QDaniel/ESPuino/src/Bluetooth.cpp

#include <Arduino.h>
#include "settings.h"

#include "Bluetooth.h"

#include "Common.h"
#include "Log.h"
#include "RotaryEncoder.h"
#include "System.h"

#include <AudioPlayer.h>

#ifdef BLUETOOTH_ENABLE
	#include "esp_bt.h"
	#include "BluetoothA2DPCommon.h"
	#include "BluetoothA2DPSink.h"
	#include "BluetoothA2DPSource.h"
	#if (defined(ESP_ARDUINO_VERSION_MAJOR) && (ESP_ARDUINO_VERSION_MAJOR >= 3))
		#include "ESP_I2S.h"
I2SClass i2s;
	#endif
#endif

#ifdef BLUETOOTH_ENABLE
	#define BLUETOOTHPLAYER_VOLUME_MAX 21u
	#define BLUETOOTHPLAYER_VOLUME_MIN 0u

BluetoothA2DPSink *a2dp_sink;
BluetoothA2DPSource *a2dp_source;
RingbufHandle_t audioSourceRingBuffer;
String btDeviceName;
#endif

#ifdef BLUETOOTH_ENABLE
const char *getType() {
	if (System_GetOperationMode() == OPMODE_BLUETOOTH_SINK) {
		return "sink";
	} else {
		return "source";
	}
}
#endif

#ifdef BLUETOOTH_ENABLE
// for esp_a2d_connection_state_t see https://docs.espressif.com/projects/esp-idf/en/latest/esp32/api-reference/bluetooth/esp_a2dp.html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
void connection_state_changed(esp_a2d_connection_state_t state, void *ptr) {
	Log_Printf(LOGLEVEL_INFO, "Bluetooth %s => connection state: %s (Free heap: %u Bytes)", getType(), ((BluetoothA2DPCommon *) ptr)->to_str(state), ESP.getFreeHeap());
	if (System_GetOperationMode() == OPMODE_BLUETOOTH_SINK) {
		// for Neopixel (indicator LEDs) use the webstream mode
		gPlayProperties.isWebstream = false;
		gPlayProperties.pausePlay = false;
		gPlayProperties.playlistFinished = true;
	}
}
#endif

#ifdef BLUETOOTH_ENABLE
// for esp_a2d_audio_state_t see https://docs.espressif.com/projects/esp-idf/en/latest/esp32/api-reference/bluetooth/esp_a2dp.html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
void audio_state_changed(esp_a2d_audio_state_t state, void *ptr) {
	Log_Printf(LOGLEVEL_INFO, "Bluetooth %s => audio state: %s (Free heap: %u Bytes)", getType(), ((BluetoothA2DPCommon *) ptr)->to_str(state), ESP.getFreeHeap());
	if (System_GetOperationMode() == OPMODE_BLUETOOTH_SINK) {
		// set play/pause status
		gPlayProperties.pausePlay = (state != ESP_A2D_AUDIO_STATE_STARTED);
		// for Neopixel (indicator LEDs) use the webstream mode
		gPlayProperties.playlistFinished = false;
		gPlayProperties.isWebstream = true;
	}
}
#endif

#ifdef BLUETOOTH_ENABLE
// handle Bluetooth AVRC metadata
// https://docs.espressif.com/projects/esp-idf/en/release-v3.2/api-reference/bluetooth/esp_avrc.html
void avrc_metadata_callback(uint8_t id, const uint8_t *text) {
	if (strlen((char *) text) == 0) {
		return;
	}
	switch (id) {
		case ESP_AVRC_MD_ATTR_TITLE:
			// title
			Log_Printf(LOGLEVEL_DEBUG, "Bluetooth => AVRC Title: %s", text);
			break;
		case ESP_AVRC_MD_ATTR_ARTIST:
			// artists
			Log_Printf(LOGLEVEL_DEBUG, "Bluetooth => AVRC Artist: %s", text);
			break;
		case ESP_AVRC_MD_ATTR_ALBUM:
			// album
			Log_Printf(LOGLEVEL_DEBUG, "Bluetooth => AVRC Album: %s", text);
			break;
		case ESP_AVRC_MD_ATTR_TRACK_NUM:
			// current track number
			Log_Printf(LOGLEVEL_DEBUG, "Bluetooth => AVRC Track-No: %s", text);
			break;
		case ESP_AVRC_MD_ATTR_NUM_TRACKS:
			// number of tracks in playlist
			Log_Printf(LOGLEVEL_DEBUG, "Bluetooth => AVRC Number of tracks: %s", text);
			break;
		case ESP_AVRC_MD_ATTR_GENRE:
			// genre
			Log_Printf(LOGLEVEL_DEBUG, "Bluetooth => AVRC Genre: %s", text);
			break;
		default:
			// unknown/unsupported metadata
			Log_Printf(LOGLEVEL_DEBUG, "Bluetooth => AVRC metadata rsp: attribute id 0x%x, %s", id, text);
			break;
	}
}
#endif

#ifdef BLUETOOTH_ENABLE
// feed the A2DP source with audio data
int32_t get_data_channels(Frame *frame, int32_t channel_len) {
	if (channel_len < 0 || frame == NULL) {
		return 0;
	}
	// Receive data from ring buffer
	size_t len {};
	vRingbufferGetInfo(audioSourceRingBuffer, nullptr, nullptr, nullptr, nullptr, &len);
	if (len < (channel_len * 4)) {
		// Serial.println("Bluetooth source => not enough data");
		return 0;
	};
	size_t sampleSize = 0;
	uint8_t *sampleBuff;
	sampleBuff = (uint8_t *) xRingbufferReceiveUpTo(audioSourceRingBuffer, &sampleSize, (TickType_t) portMAX_DELAY, channel_len * 4);
	if (sampleBuff != NULL) {
		// fill the channel data
		for (int sample = 0; sample < (channel_len); ++sample) {
			frame[sample].channel1 = (sampleBuff[sample * 4 + 3] << 8) | sampleBuff[sample * 4 + 2];
			frame[sample].channel2 = (sampleBuff[sample * 4 + 1] << 8) | sampleBuff[sample * 4];
		};
		vRingbufferReturnItem(audioSourceRingBuffer, (void *) sampleBuff);
	};
	// avoid WDT reset & give audio/other tasks some CPU time
	vTaskDelay(portTICK_PERIOD_MS * 1);
	return channel_len;
};
#endif

#ifdef BLUETOOTH_ENABLE
// callback which is notified on update Receiver RSSI
void rssi(esp_bt_gap_cb_param_t::read_rssi_delta_param &rssiParam) {
	Log_Printf(LOGLEVEL_DEBUG, "Bluetooth => RSSI value: %d", rssiParam.rssi_delta);
}
#endif

#ifdef BLUETOOTH_ENABLE
// Callback notifying BT-source devices available.
// Return true to connect, false will continue scanning
bool scan_bluetooth_device_callback(const char *ssid, esp_bd_addr_t address, int rssi) {
	Log_Printf(LOGLEVEL_INFO, "Bluetooth source => Device found: %s", ssid);

	if (btDeviceName == "") {
		// no device name given, connect to first device found
		return true;
	} else {
		// connect if device name (partially) matching, todo: compare case insensitive here?
		return startsWith(ssid, btDeviceName.c_str());
	}
}
#endif

void Bluetooth_VolumeChanged(int _newVolume) {
#ifdef BLUETOOTH_ENABLE
	if ((_newVolume < 0) || (_newVolume > 0x7F)) {
		return;
	}
	// map bluetooth volume (0..127) to ESPuino volume (0..21) to
	uint8_t _volume;
	_volume = map(_newVolume, 0, 0x7F, BLUETOOTHPLAYER_VOLUME_MIN, BLUETOOTHPLAYER_VOLUME_MAX);
	if (AudioPlayer_GetCurrentVolume() != _volume) {
		Log_Printf(LOGLEVEL_INFO, "Bluetooth => volume changed:  %d !", _volume);
		AudioPlayer_VolumeToQueueSender(_volume, true);
	}
#endif
}

void Bluetooth_Init(void) {
#ifdef BLUETOOTH_ENABLE
	if (System_GetOperationMode() == OPMODE_BLUETOOTH_SINK) {
		// bluetooth in sink mode (player acts as a BT-Speaker)
		a2dp_sink = new BluetoothA2DPSink();
	#if (defined(ESP_ARDUINO_VERSION_MAJOR) && (ESP_ARDUINO_VERSION_MAJOR >= 3))
		i2s.setPins(I2S_BCLK, I2S_LRC, I2S_DOUT);
		if (!i2s.begin(I2S_MODE_STD, 44100, I2S_DATA_BIT_WIDTH_16BIT, I2S_SLOT_MODE_STEREO, I2S_STD_SLOT_BOTH)) {
			Log_Println("Failed to initialize I2S!", LOGLEVEL_ERROR);
			while (1)
				; // do nothing
		}
		a2dp_sink->set_output(i2s);
	#else
		i2s_pin_config_t pin_config = {
		#if ESP_IDF_VERSION >= ESP_IDF_VERSION_VAL(4, 0, 0)
			.mck_io_num = 0,
		#endif
			.bck_io_num = I2S_BCLK,
			.ws_io_num = I2S_LRC,
			.data_out_num = I2S_DOUT,
			.data_in_num = I2S_PIN_NO_CHANGE
		};
		a2dp_sink->set_pin_config(pin_config);
	#endif
		a2dp_sink->set_rssi_callback(rssi);
		a2dp_sink->activate_pin_code(false);
		if (gPrefsSettings.getBool("playMono", false)) {
			a2dp_sink->set_mono_downmix(true);
		}
		a2dp_sink->set_auto_reconnect(true);
		a2dp_sink->set_rssi_active(true);
		// start bluetooth sink
		a2dp_sink->start(nameBluetoothSinkDevice);
		Log_Printf(LOGLEVEL_INFO, "Bluetooth sink started, Device: %s", nameBluetoothSinkDevice);
		// connect events after startup
		a2dp_sink->set_on_connection_state_changed(connection_state_changed, a2dp_sink);
		a2dp_sink->set_on_audio_state_changed(audio_state_changed, a2dp_sink);
		a2dp_sink->set_avrc_metadata_callback(avrc_metadata_callback);
		a2dp_sink->set_on_volumechange(Bluetooth_VolumeChanged);
	} else if (System_GetOperationMode() == OPMODE_BLUETOOTH_SOURCE) {
		// create audio source ringbuffer on demand
		audioSourceRingBuffer = xRingbufferCreate(8192, RINGBUF_TYPE_BYTEBUF);
		if (audioSourceRingBuffer == NULL) {
			Log_Println("cannot create audioSourceRingBuffer!", LOGLEVEL_ERROR);
		}
		//  setup BT source
		a2dp_source = new BluetoothA2DPSource();

		// a2dp_source->set_auto_reconnect(false);   // auto reconnect
		// a2dp_source->set_task_core(1);            // task core
		// a2dp_source->set_nvs_init(true);          // erase/initialize NVS
		// a2dp_source->set_ssp_enabled(true);       // enable secure simple pairing

		// pairing pin-code, see https://forum.espuino.de/t/neues-feature-bluetooth-kopfhoerer/1293/30
		String btPinCode = gPrefsSettings.getString("btPinCode", "");
		if (btPinCode != "") {
			a2dp_source->set_ssp_enabled(true);
			a2dp_source->set_pin_code(btPinCode.c_str());
		}
		// start bluetooth source
		a2dp_source->set_ssid_callback(scan_bluetooth_device_callback);
		a2dp_source->start(get_data_channels);
		// get device name
		btDeviceName = "";
		if (gPrefsSettings.isKey("btDeviceName")) {
			btDeviceName = gPrefsSettings.getString("btDeviceName", "");
		}
		Log_Printf(LOGLEVEL_INFO, "Bluetooth source started, connect to device: '%s'", (btDeviceName == "") ? "connect to first device found" : btDeviceName.c_str());
		// connect events after startup
		a2dp_source->set_on_connection_state_changed(connection_state_changed, a2dp_source);
		a2dp_source->set_on_audio_state_changed(audio_state_changed, a2dp_source);
		// max headphone volume (0..255): volume is controlled by audio class
		a2dp_source->set_volume(127);
	} else {
		esp_bt_mem_release(ESP_BT_MODE_BTDM);
	}
#endif
}

void Bluetooth_Cyclic(void) {
#ifdef BLUETOOTH_ENABLE
	if ((System_GetOperationMode() == OPMODE_BLUETOOTH_SINK) && (a2dp_sink)) {
		esp_a2d_audio_state_t state = a2dp_sink->get_audio_state();
		// Reset Sleep Timer when audio is playing
		if (state == ESP_A2D_AUDIO_STATE_STARTED) {
			System_UpdateActivityTimer();
		}
	}
	if ((System_GetOperationMode() == OPMODE_BLUETOOTH_SOURCE) && (a2dp_source)) {
		esp_a2d_audio_state_t state = a2dp_source->get_audio_state();
		// Reset Sleep Timer when audio is playing
		if (state == ESP_A2D_AUDIO_STATE_STARTED) {
			System_UpdateActivityTimer();
		}
	}
#endif
}

void Bluetooth_PlayPauseTrack(void) {
#ifdef BLUETOOTH_ENABLE
	if ((System_GetOperationMode() == OPMODE_BLUETOOTH_SINK) && (a2dp_sink)) {
		esp_a2d_audio_state_t state = a2dp_sink->get_audio_state();
		if (state == ESP_A2D_AUDIO_STATE_STARTED) {
			a2dp_sink->play();
		} else {
			a2dp_sink->pause();
		}
	}
#endif
}

void Bluetooth_NextTrack(void) {
#ifdef BLUETOOTH_ENABLE
	if ((System_GetOperationMode() == OPMODE_BLUETOOTH_SINK) && (a2dp_sink)) {
		a2dp_sink->next();
	}
#endif
}

void Bluetooth_PreviousTrack(void) {
#ifdef BLUETOOTH_ENABLE
	if ((System_GetOperationMode() == OPMODE_BLUETOOTH_SINK) && (a2dp_sink)) {
		a2dp_sink->previous();
	}
#endif
}

// set volume from ESPuino to phone needs at least Arduino ESP version 2.0.0
void Bluetooth_SetVolume(const int32_t _newVolume, bool reAdjustRotary) {
#ifdef BLUETOOTH_ENABLE
	if (!a2dp_sink) {
		return;
	}
	uint8_t _volume;
	if (_newVolume < int32_t(BLUETOOTHPLAYER_VOLUME_MIN)) {
		return;
	} else if (_newVolume > BLUETOOTHPLAYER_VOLUME_MAX) {
		return;
	} else {
		// map ESPuino min/max volume (0..21) to bluetooth volume (0..127)
		_volume = map(_newVolume, BLUETOOTHPLAYER_VOLUME_MIN, BLUETOOTHPLAYER_VOLUME_MAX, 0, 0x7F);
		a2dp_sink->set_volume(_volume);
		if (reAdjustRotary) {
			RotaryEncoder_Readjust();
		}
	}
#endif
}

bool Bluetooth_Source_SendAudioData(int16_t *outBuff, uint16_t validSamples) {
#ifdef BLUETOOTH_ENABLE
	// send audio data to ringbuffer
	if ((System_GetOperationMode() == OPMODE_BLUETOOTH_SOURCE) && (a2dp_source) && (validSamples > 0) && a2dp_source->is_connected()) {
		return (pdTRUE == xRingbufferSend(audioSourceRingBuffer, outBuff, sizeof(uint32_t) * validSamples, (TickType_t) portMAX_DELAY));
	} else {
		return false;
	}
#else
	return false;
#endif
}

bool Bluetooth_Device_Connected() {
#ifdef BLUETOOTH_ENABLE
	// send audio data to ringbuffer
	return (((System_GetOperationMode() == OPMODE_BLUETOOTH_SINK) && (a2dp_sink) && a2dp_sink->is_connected()) || ((System_GetOperationMode() == OPMODE_BLUETOOTH_SOURCE) && (a2dp_source) && a2dp_source->is_connected()));
#else
	return false;
#endif
}
