QDaniel/ESPuino/src/System.cpp

#include <Arduino.h>
#include "settings.h"

#include "System.h"

#include "Audio.h"
#include "AudioPlayer.h"
#include "Led.h"
#include "Log.h"
#include "Mqtt.h"
#include "Port.h"
#include "Power.h"
#include "Rfid.h"
#include "SdCard.h"
#include "esp_system.h"
#include "freertos/FreeRTOS.h"
#include "freertos/task.h"

#include <esp_random.h>

constexpr const char prefsRfidNamespace[] = "rfidTags"; // Namespace used to save IDs of rfid-tags
constexpr const char prefsSettingsNamespace[] = "settings"; // Namespace used for generic settings

Preferences gPrefsRfid;
Preferences gPrefsSettings;

unsigned long System_LastTimeActiveTimestamp = 0u; // Timestamp of last user-interaction
unsigned long System_SleepTimerStartTimestamp = 0u; // Flag if sleep-timer is active
bool System_GoToSleep = false; // Flag for turning uC immediately into deepsleep
bool System_Sleeping = false; // Flag for turning into deepsleep is in progress
bool System_LockControls = false; // Flag if buttons and rotary encoder is locked
uint8_t System_MaxInactivityTime = 10u; // Time in minutes, after uC is put to deep sleep because of inactivity (and modified later via GUI)
uint8_t System_SleepTimer = 30u; // Sleep timer in minutes that can be optionally used (and modified later via MQTT or RFID)

// Operation Mode
volatile uint8_t System_OperationMode;

void System_SleepHandler(void);
void System_DeepSleepManager(void);

// Init only NVS required for LPCD
void System_Init_LPCD(void) {
#ifdef PN5180_ENABLE_LPCD
	gPrefsRfid.begin(prefsRfidNamespace);
#endif
}

void System_Init(void) {
	srand(esp_random());

#ifndef PN5180_ENABLE_LPCD
	gPrefsRfid.begin(prefsRfidNamespace);
#endif
	gPrefsSettings.begin(prefsSettingsNamespace);

	// Get maximum inactivity-time from NVS
	uint32_t nvsMInactivityTime = gPrefsSettings.getUInt("mInactiviyT", 0);
	if (nvsMInactivityTime) {
		System_MaxInactivityTime = nvsMInactivityTime;
		Log_Printf(LOGLEVEL_INFO, restoredMaxInactivityFromNvs, nvsMInactivityTime);
	} else {
		gPrefsSettings.putUInt("mInactiviyT", System_MaxInactivityTime);
		Log_Println(wroteMaxInactivityToNvs, LOGLEVEL_ERROR);
	}

	System_OperationMode = gPrefsSettings.getUChar("operationMode", OPMODE_NORMAL);
}

void System_Cyclic(void) {
	System_SleepHandler();
	System_DeepSleepManager();
}

void System_UpdateActivityTimer(void) {
	System_LastTimeActiveTimestamp = millis();
}

void System_RequestSleep(void) {
	System_GoToSleep = true;
}

bool System_SetSleepTimer(uint8_t minutes) {
	bool sleepTimerEnabled = false;

	if (System_SleepTimerStartTimestamp && (System_SleepTimer == minutes)) {
		System_SleepTimerStartTimestamp = 0u;
		System_SleepTimer = 0u;
		Led_SetNightmode(false);
		Log_Println(modificatorSleepd, LOGLEVEL_NOTICE);
	} else {
		System_SleepTimerStartTimestamp = millis();
		System_SleepTimer = minutes;
		sleepTimerEnabled = true;

		Led_SetNightmode(true);
		if (minutes == 15) {
			Log_Println(modificatorSleepTimer15, LOGLEVEL_NOTICE);
		} else if (minutes == 30) {
			Log_Println(modificatorSleepTimer30, LOGLEVEL_NOTICE);
		} else if (minutes == 60) {
			Log_Println(modificatorSleepTimer60, LOGLEVEL_NOTICE);
		} else {
			Log_Println(modificatorSleepTimer120, LOGLEVEL_NOTICE);
		}
	}

#ifdef MQTT_ENABLE
	publishMqtt(topicSleepTimerState, System_GetSleepTimer(), false);
#endif

	return sleepTimerEnabled;
}

void System_DisableSleepTimer(void) {
	System_SleepTimerStartTimestamp = 0u;
	Led_SetNightmode(false);
}

bool System_IsSleepTimerEnabled(void) {
	return (System_SleepTimerStartTimestamp > 0u || gPlayProperties.sleepAfterCurrentTrack || gPlayProperties.sleepAfterPlaylist || gPlayProperties.playUntilTrackNumber);
}

uint32_t System_GetSleepTimerTimeStamp(void) {
	return System_SleepTimerStartTimestamp;
}

bool System_IsSleepPending(void) {
	return System_Sleeping;
}

uint8_t System_GetSleepTimer(void) {
	return System_SleepTimer;
}

void System_SetLockControls(bool value) {
	System_LockControls = value;
}

void System_ToggleLockControls(void) {
	System_LockControls = !System_LockControls;
}

bool System_AreControlsLocked(void) {
	return System_LockControls;
}

void System_IndicateError(void) {
	Led_Indicate(LedIndicatorType::Error);
}

void System_IndicateOk(void) {
	Led_Indicate(LedIndicatorType::Ok);
}

// Writes to NVS, if bluetooth or "normal" mode is desired
void System_SetOperationMode(uint8_t opMode) {
	uint8_t currentOperationMode = gPrefsSettings.getUChar("operationMode", OPMODE_NORMAL);
	if (currentOperationMode != opMode) {
		if (gPrefsSettings.putUChar("operationMode", opMode)) {
			Log_Println(restartAfterOperationModeChange, LOGLEVEL_INFO);
			ESP.restart();
		}
	}
}

uint8_t System_GetOperationMode(void) {
	return System_OperationMode;
}

// Reads from NVS, if bluetooth or "normal" mode is desired
uint8_t System_GetOperationModeFromNvs(void) {
	return gPrefsSettings.getUChar("operationMode", OPMODE_NORMAL);
}

// Sets deep-sleep-flag if max. inactivity-time is reached
void System_SleepHandler(void) {
	unsigned long m = millis();
	if (m >= System_LastTimeActiveTimestamp && (m - System_LastTimeActiveTimestamp >= (System_MaxInactivityTime * 1000u * 60u))) {
		Log_Println(goToSleepDueToIdle, LOGLEVEL_INFO);
		System_RequestSleep();
	} else if (System_SleepTimerStartTimestamp > 00) {
		if (m - System_SleepTimerStartTimestamp >= (System_SleepTimer * 1000u * 60u)) {
			Log_Println(goToSleepDueToTimer, LOGLEVEL_INFO);
			System_RequestSleep();
		}
	}
}

// prepare power down
void System_PreparePowerDown(void) {

	AudioPlayer_Exit();
// Disable amps in order to avoid ugly noises when powering off
#ifdef GPIO_PA_EN
	Log_Println("shutdown amplifier..", LOGLEVEL_NOTICE);
	Port_Write(GPIO_PA_EN, false, false);
#endif
#ifdef GPIO_HP_EN
	Log_Println("shutdown headphone..", LOGLEVEL_NOTICE);
	Port_Write(GPIO_HP_EN, false, false);
#endif

	Mqtt_Exit();
	Led_Exit();

	if (gPrefsSettings.getBool("recoverVolBoot", false)) {
		gPrefsSettings.putUInt("previousVolume", AudioPlayer_GetCurrentVolume());
	}
	SdCard_Exit();

	Serial.flush();
}

void System_Restart(void) {
	// prepare power down (shutdown common modules)
	System_PreparePowerDown();
	// restart the ESP-32
	Log_Println("restarting..", LOGLEVEL_NOTICE);
	ESP.restart();
}

// Puts uC to deep-sleep if flag is set
void System_DeepSleepManager(void) {
	if (System_GoToSleep) {
		if (System_Sleeping) {
			return;
		}

		System_Sleeping = true;
		Log_Println(goToSleepNow, LOGLEVEL_NOTICE);
		// prepare power down (shutdown common modules)
		System_PreparePowerDown();
		// switch off power
		Power_PeripheralOff();
		// time to settle down..
		delay(200);
// .. for LPCD
#if defined(RFID_READER_TYPE_MFRC522_SPI) || defined(RFID_READER_TYPE_MFRC522_I2C) || defined(RFID_READER_TYPE_PN5180)
		Rfid_Exit();
#endif
#ifdef PORT_EXPANDER_ENABLE
		Port_Exit();
#endif
		// goto sleep now
		Log_Println("deep-sleep, good night.......", LOGLEVEL_NOTICE);
		esp_deep_sleep_start();
	}
}

// Print the wake-up reason why ESP32 is awake now
void System_ShowWakeUpReason() {
	esp_sleep_wakeup_cause_t wakeup_reason;
	wakeup_reason = esp_sleep_get_wakeup_cause();

	switch (wakeup_reason) {
		case ESP_SLEEP_WAKEUP_EXT0:
			Log_Println("Wakeup caused by push-button", LOGLEVEL_NOTICE);
			break;
		case ESP_SLEEP_WAKEUP_EXT1:
			Log_Println("Wakeup caused by low power card-detection", LOGLEVEL_NOTICE);
			break;
		case ESP_SLEEP_WAKEUP_TIMER:
			Log_Println("Wakeup caused by timer", LOGLEVEL_NOTICE);
			break;
		case ESP_SLEEP_WAKEUP_TOUCHPAD:
			Log_Println("Wakeup caused by touchpad", LOGLEVEL_NOTICE);
			break;
		case ESP_SLEEP_WAKEUP_ULP:
			Log_Println("Wakeup caused by ULP-program", LOGLEVEL_NOTICE);
			break;
		default:
			Log_Printf(LOGLEVEL_NOTICE, "Wakeup was not caused by deepsleep: %d", wakeup_reason);
			break;
	}
}

void System_esp_print_tasks(void) {
#ifdef CONFIG_FREERTOS_USE_TRACE_FACILITY
	char *pbuffer = (char *) calloc(2048, 1);
	vTaskGetRunTimeStats(pbuffer);
	Serial.printf("=====\n%s\n=====", pbuffer);
	free(pbuffer);
#else
	Serial.println("Enable CONFIG_FREERTOS_USE_TRACE_FACILITY to use vTaskGetRunTimeStats()!");
#endif
}
