QDaniel/ESPuino/src/RfidCommon.cpp

#include <Arduino.h>
#include "settings.h"

#include "AudioPlayer.h"
#include "Cloud.h"
#include "Cmd.h"
#include "Common.h"
#include "Log.h"
#include "MemX.h"
#include "Mqtt.h"
#include "Queues.h"
#include "Rfid.h"
#include "System.h"
#include "Web.h"

unsigned long Rfid_LastRfidCheckTimestamp = 0;
char gCurrentRfidTagId[cardIdStringSize] = ""; // No crap here as otherwise it could be shown in GUI
#ifdef DONT_ACCEPT_SAME_RFID_TWICE_ENABLE
char gOldRfidTagId[cardIdStringSize] = "X"; // Init with crap
#endif

// check if we have RFID-reader enabled
#if defined(RFID_READER_TYPE_MFRC522_SPI) || defined(RFID_READER_TYPE_MFRC522_I2C) || defined(RFID_READER_TYPE_PN5180)
	#define RFID_READER_ENABLED 1
#endif

// Tries to lookup RFID-tag-string in NVS and extracts parameter from it if found
void Rfid_PreferenceLookupHandler(void) {
#if defined(RFID_READER_ENABLED)
	BaseType_t rfidStatus;
	char rfidTagId[cardIdStringSize];
	char _file[255];
	uint32_t _lastPlayPos = 0;
	uint16_t _trackLastPlayed = 0;
	uint32_t _playMode = 1;

	rfidStatus = xQueueReceive(gRfidCardQueue, &rfidTagId, 0);
	if (rfidStatus == pdPASS) {
		System_UpdateActivityTimer();
		strncpy(gCurrentRfidTagId, rfidTagId, cardIdStringSize - 1);
		Log_Printf(LOGLEVEL_INFO, "%s: %s", rfidTagReceived, gCurrentRfidTagId);
		Web_SendWebsocketData(0, WebsocketCodeType::CurrentRfid); // Push new rfidTagId to all websocket-clients
		String s = "-1";
		if (gPrefsRfid.isKey(gCurrentRfidTagId)) {
			s = gPrefsRfid.getString(gCurrentRfidTagId, "-1"); // Try to lookup rfidId in NVS
		}
		if (!s.compareTo("-1")) {
			if (Cloud_Scan(gCurrentRfidTagId)) {
				return;
			}
			Log_Println(rfidTagUnknownInNvs, LOGLEVEL_ERROR);
			System_IndicateError();
			// allow to escape from bluetooth mode with an unknown card, switch back to normal mode
			System_SetOperationMode(OPMODE_NORMAL);
			return;
		}

		char *token;
		uint8_t i = 1;
		token = strtok((char *) s.c_str(), stringDelimiter);
		while (token != NULL) { // Try to extract data from string after lookup
			if (i == 1) {
				strncpy(_file, token, sizeof(_file) / sizeof(_file[0]));
			} else if (i == 2) {
				_lastPlayPos = strtoul(token, NULL, 10);
			} else if (i == 3) {
				_playMode = strtoul(token, NULL, 10);
			} else if (i == 4) {
				_trackLastPlayed = strtoul(token, NULL, 10);
			}
			i++;
			token = strtok(NULL, stringDelimiter);
		}

		if (i != 5) {
			Log_Println(errorOccuredNvs, LOGLEVEL_ERROR);
			System_IndicateError();
		} else {
			// Only pass file to queue if strtok revealed 3 items
			if (_playMode >= 100) {
				// Modification-cards can change some settings (e.g. introducing track-looping or sleep after track/playlist).
				Cmd_Action(_playMode);
			} else {
	#ifdef DONT_ACCEPT_SAME_RFID_TWICE_ENABLE
				if (strncmp(gCurrentRfidTagId, gOldRfidTagId, 12) == 0) {
					Log_Printf(LOGLEVEL_ERROR, dontAccepctSameRfid, gCurrentRfidTagId);
					// System_IndicateError(); // Enable to have shown error @neopixel every time
					return;
				} else {
					strncpy(gOldRfidTagId, gCurrentRfidTagId, 12);
				}
	#endif
	#ifdef MQTT_ENABLE
				publishMqtt(topicRfidState, gCurrentRfidTagId, false);
	#endif

	#ifdef BLUETOOTH_ENABLE
				// if music rfid was read, go back to normal mode
				if (System_GetOperationMode() == OPMODE_BLUETOOTH_SINK) {
					System_SetOperationMode(OPMODE_NORMAL);
				}
	#endif

				AudioPlayer_TrackQueueDispatcher(_file, _lastPlayPos, _playMode, _trackLastPlayed);
			}
		}
	}
#endif
}

#ifdef DONT_ACCEPT_SAME_RFID_TWICE_ENABLE
void Rfid_ResetOldRfid() {
	strncpy(gOldRfidTagId, "X", cardIdStringSize - 1);
}
#endif

#if defined(RFID_READER_ENABLED)
extern TaskHandle_t rfidTaskHandle;
#endif

void Rfid_TaskPause(void) {
#if defined(RFID_READER_ENABLED)
	vTaskSuspend(rfidTaskHandle);
#endif
}
void Rfid_TaskResume(void) {
#if defined(RFID_READER_ENABLED)
	vTaskResume(rfidTaskHandle);
#endif
}
